pixzrr/SuiveurDeLigne/TP2_GABOU_PORTIER/actions_elementaires.h

#ifndef actions_elementaires_h
  #define actions_elementaires_h

  #include <Arduino.h>
  #include "connexions_robot_arduino_uno.h"

  //Prototypes des fonctions 
  void attendre_START(void);
  void affiche_tention_batterie(void);

#endif
